charleslemaux/odoo-epaper-dashboard/src/app/time_fmt.c

/*
** Charles Le Maux, 2026
** epaper_dashboard
** File description:
** Date and time formatting helpers plus deadline classification
*/

#include <stdio.h>
#include <stdlib.h>
#include <string.h>
#include "time_fmt.h"

static const char *DAY_NAMES[7] = {
    "dim", "lun", "mar", "mer", "jeu", "ven", "sam"
};

void time_fmt_banner(char *dst, size_t size, struct tm const *lt)
{
    snprintf(dst, size, "%s %02d/%02d", DAY_NAMES[lt->tm_wday % 7],
        lt->tm_mday, lt->tm_mon + 1);
}

void time_fmt_hhmm(char *dst, size_t size, struct tm const *lt)
{
    snprintf(dst, size, "%02d:%02d", lt->tm_hour, lt->tm_min);
}

void time_fmt_ddmm(char *dst, size_t size, char const *iso)
{
    if (iso == 0 || strlen(iso) < 10) {
        snprintf(dst, size, "--");
        return;
    }
    snprintf(dst, size, "%c%c/%c%c", iso[8], iso[9], iso[5], iso[6]);
}

/*
** struct tm fields are plain int with no compile-time bound, so GCC's
** -Wformat-truncation cannot prove the (always-small) year/month/day
** values fit; the pragma below is the standard, localized workaround,
** guarded to real GCC since Clang has no -Wformat-truncation.
*/
static void make_iso(char *dst, size_t size, struct tm const *t)
{
    #if defined(__GNUC__) && !defined(__clang__)
        #pragma GCC diagnostic push
        #pragma GCC diagnostic ignored "-Wformat-truncation"
    #endif
    snprintf(dst, size, "%04d-%02d-%02d", t->tm_year + 1900,
        t->tm_mon + 1, t->tm_mday);
    #if defined(__GNUC__) && !defined(__clang__)
        #pragma GCC diagnostic pop
    #endif
}

static int parse_iso(char const *iso, struct tm *out)
{
    if (strlen(iso) < 10 || iso[4] != '-' || iso[7] != '-')
        return -1;
    out->tm_year = atoi(iso) - 1900;
    out->tm_mon = atoi(iso + 5) - 1;
    out->tm_mday = atoi(iso + 8);
    return 0;
}

int time_fmt_days_late(char const *iso, struct tm const *today)
{
    struct tm due = {0};
    struct tm now = *today;

    if (iso == 0 || parse_iso(iso, &due) != 0)
        return 0;
    due.tm_hour = 12;
    due.tm_isdst = -1;
    now.tm_hour = 12;
    now.tm_min = 0;
    now.tm_sec = 0;
    now.tm_isdst = -1;
    return (int)((mktime(&now) - mktime(&due)) / 86400);
}

int time_fmt_deadline_class(char const *iso, struct tm const *today)
{
    char today_iso[11];
    char tomorrow_iso[11];
    struct tm tomorrow = *today;

    if (iso == 0 || iso[0] == '\0')
        return DL_NONE;
    tomorrow.tm_mday++;
    mktime(&tomorrow);
    make_iso(today_iso, sizeof(today_iso), today);
    make_iso(tomorrow_iso, sizeof(tomorrow_iso), &tomorrow);
    if (strncmp(iso, today_iso, 10) < 0)
        return DL_OVERDUE;
    if (strncmp(iso, tomorrow_iso, 10) <= 0)
        return DL_SOON;
    return DL_NORMAL;
}
